abkfenris/gage-particle/src/distance_sensor.h

/**
 * Read from Maxbotix ultrasonic sensor
 * 
 * @author Alex Kerney
 */
#ifndef DistanceSensor_h
#define DistanceSensor_h

#include "Particle.h"
#include "stats/Statistics.h"

#include "sensor.h"

// Number of samples that should be kept in the statistics history
const int NUMBER_OF_SAMPLES = 20;

/**
 * Maxbotix Distance Sensor
 */
class DistanceSensor : public Sensor
{
private:
    /**
     * Running statistics of samples that are collected at the sensor update frequency
     */
    Statistics stats;
    // Milliseconds when the sensor was last read
    int last_update_ms;

public:
    DistanceSensor();

    /**
     * Starts the serial connection to the ultrasonic sensor,
     * and sets the update timing
     */
    void setup();

    // Reads the sensor once every 200 ms
    void loop();

    // Return the millimeters from the sensor
    int read_sensor();

    // Return the mean of the last 20 samples
    float value();
    // Return the current standard deviation
    float std_deviation();
};

#endif
