abkfenris/gage-particle/src/sensor/grove_temp.cpp

#include "sensor/grove_temp.h"

#define MINIMUM_BETWEEN_READINGS_MS 10000

GroveTempSensor::GroveTempSensor(byte dhtPin) : dht(dhtPin)
{
    last_update_ms = millis() - MINIMUM_BETWEEN_READINGS_MS;
}

void GroveTempSensor::setup()
{
    dht.begin();
}

void GroveTempSensor::loop()
{
    if (millis() - last_update_ms >= MINIMUM_BETWEEN_READINGS_MS)
    {
        last_update_ms = millis();
        last_temp_f = dht.getTempFarenheit();
        DataLog.add_value("temperature", value());
    }
}

float GroveTempSensor::value()
{
    return last_temp_f;
}
